Miguel-Sangel/Robot-Equilibrista/html/P2.jpg

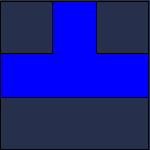
html/P2.jpg
