Miguel-Sangel/Robot-Equilibrista/src/html/FLECHA-A.jpg

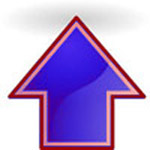
src/html/FLECHA-A.jpg
