Miguel-Sangel/Robot-Equilibrista/src/html/GIRO-I.jpg

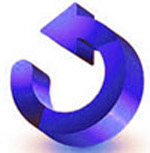
src/html/GIRO-I.jpg
