Miguel-Sangel/Robot-Equilibrista/src/html/P3.jpg

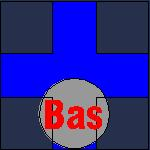
src/html/P3.jpg
