Miguel-Sangel/Robot-Equilibrista/src/html/P5.jpg

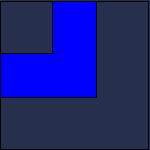
src/html/P5.jpg
