Miguel-Sangel/Robot-Equilibrista/src/html/STOP.jpg

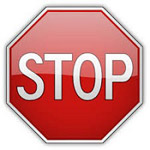
src/html/STOP.jpg
